AugustoS97/Raspberry-Pi-NAS/3D Model/RENDER/NAS_Servidor_con_OLED_2022-Apr-14_10-37-46PM-000_CustomizedView1304364207_png.png

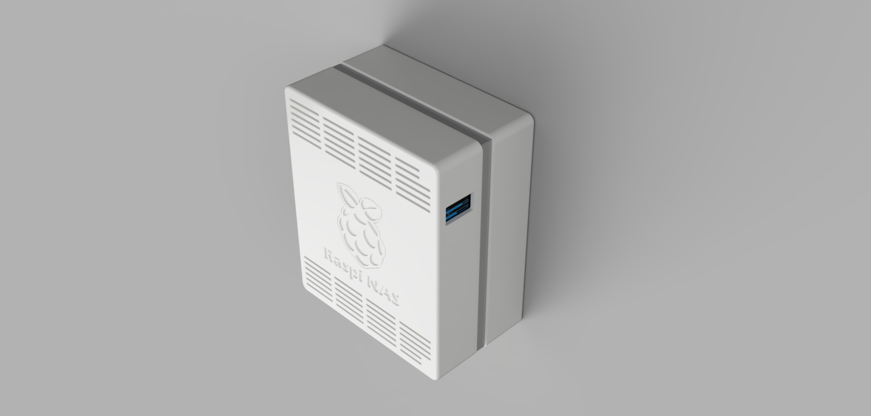
3D Model/RENDER/NAS_Servidor_con_OLED_2022-Apr-14_10-37-46PM-000_CustomizedView1304364207_png.png
