AugustoS97/Raspberry-Pi-NAS/Photos/NAS_interior.jpg

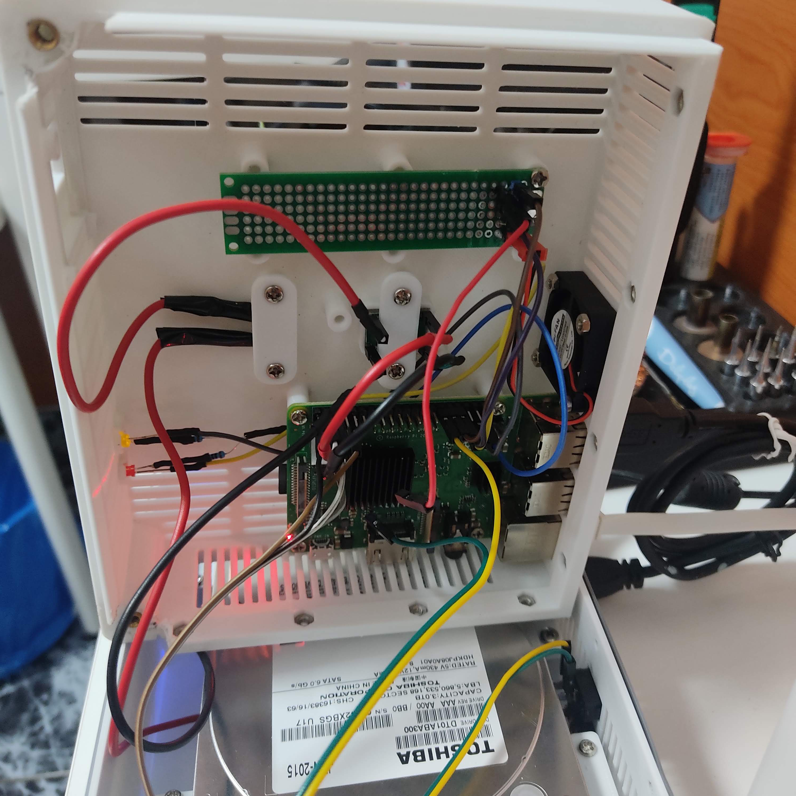
Photos/NAS_interior.jpg
