AugustoS97/Raspberry-Pi-NAS/Photos/NAS_interior_2.jpg

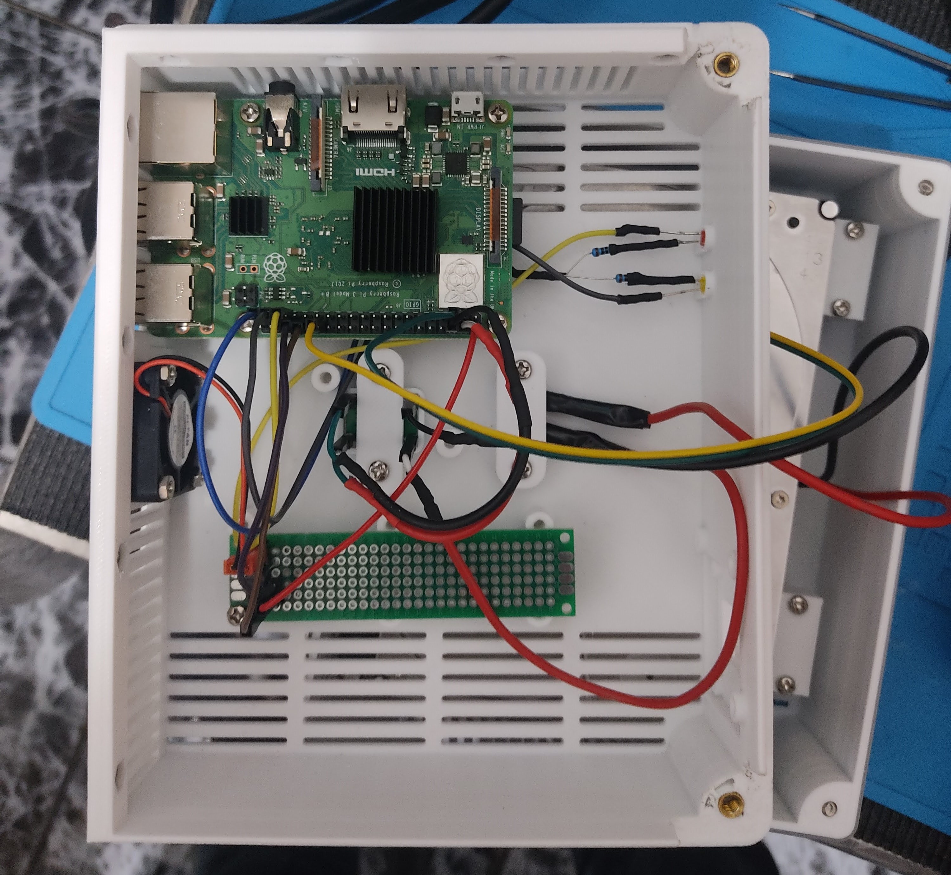
Photos/NAS_interior_2.jpg
